datleminh5173-sys/ugv/ugv_jga25_v2/preview_ball_socket_fixed.png

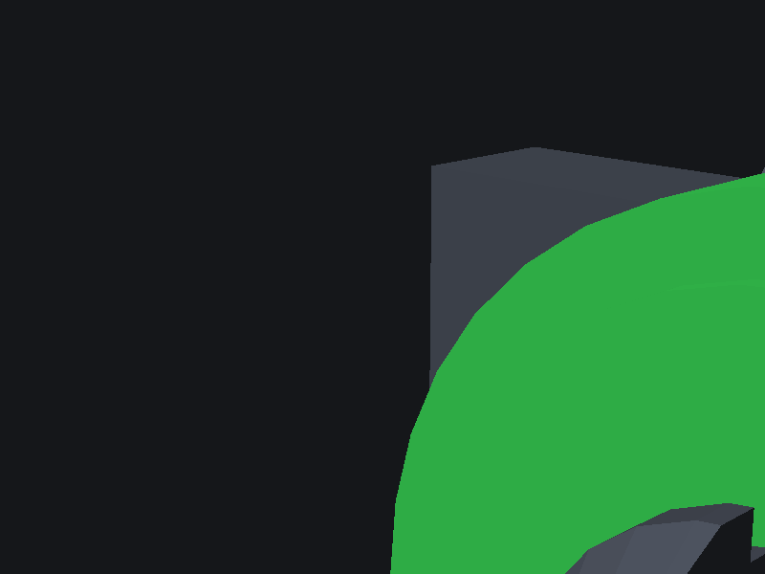
ugv_jga25_v2/preview_ball_socket_fixed.png
