datleminh5173-sys/ugv/ugv_jga25_v2/preview_ball_stud_angled.png

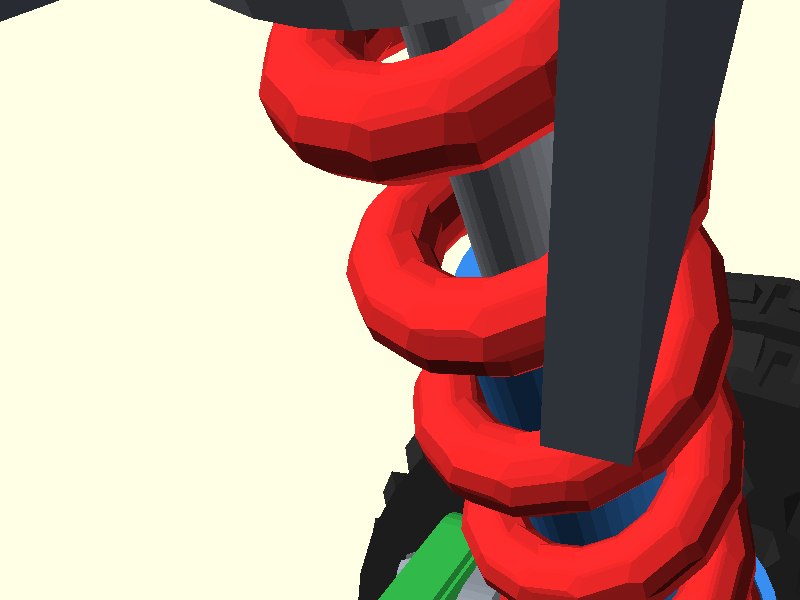
ugv_jga25_v2/preview_ball_stud_angled.png
