datleminh5173-sys/ugv/ugv_jga25_v2/preview_chot_snap_pin_single.png

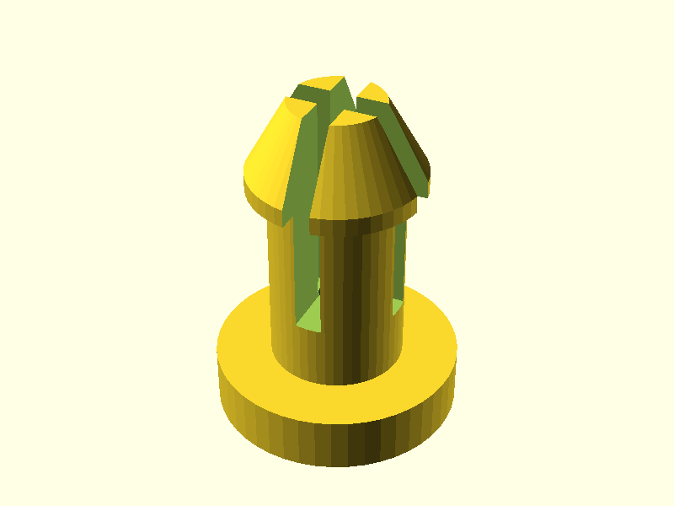
ugv_jga25_v2/preview_chot_snap_pin_single.png
