datleminh5173-sys/ugv/ugv_jga25_v2/preview_khop_cau_full_xe.png

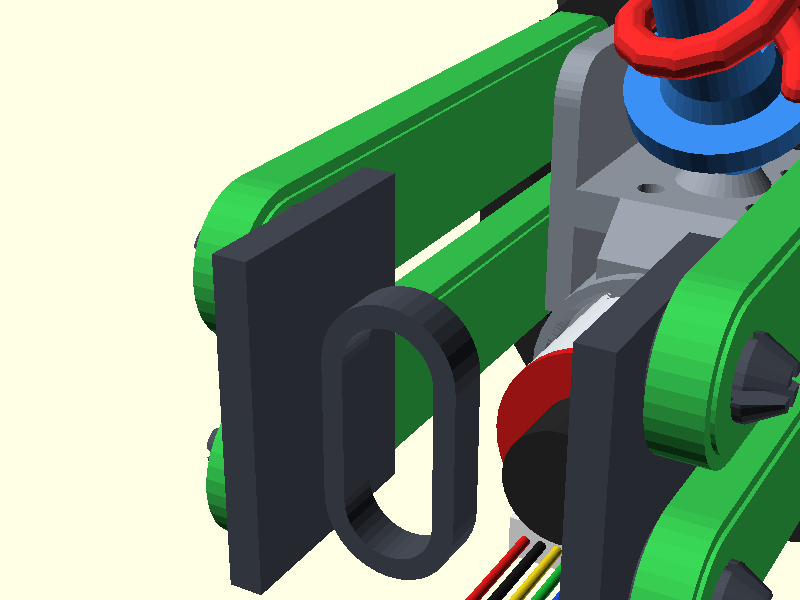
ugv_jga25_v2/preview_khop_cau_full_xe.png
