datleminh5173-sys/ugv/ugv_jga25_v2/preview_no_handles.png

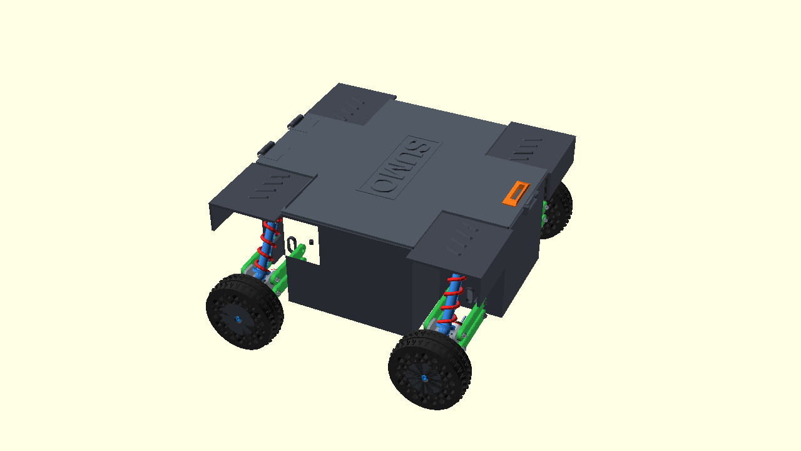
ugv_jga25_v2/preview_no_handles.png
