datleminh5173-sys/ugv/ugv_jga25_v2/preview_phuoc_khop_cau_bottom.png

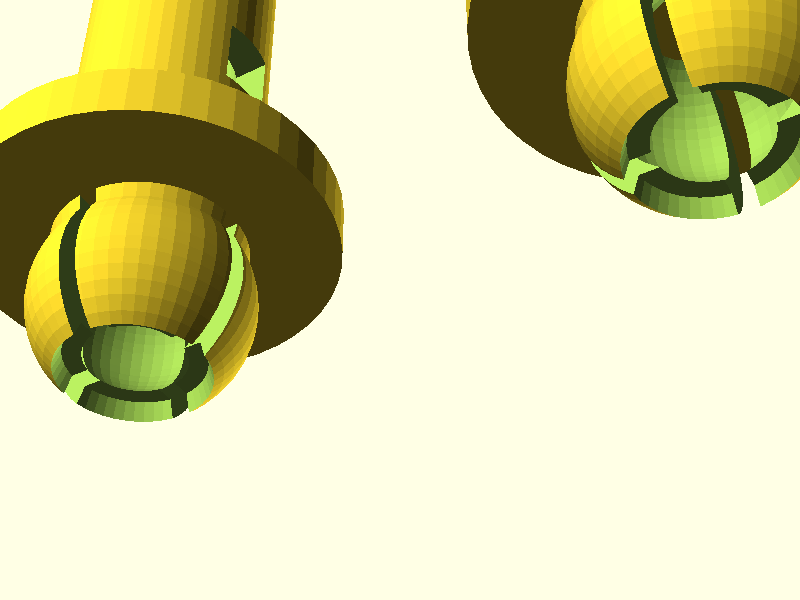
ugv_jga25_v2/preview_phuoc_khop_cau_bottom.png
