datleminh5173-sys/ugv/ugv_jga25_v2/preview_phuoc_snap_pin_close.png

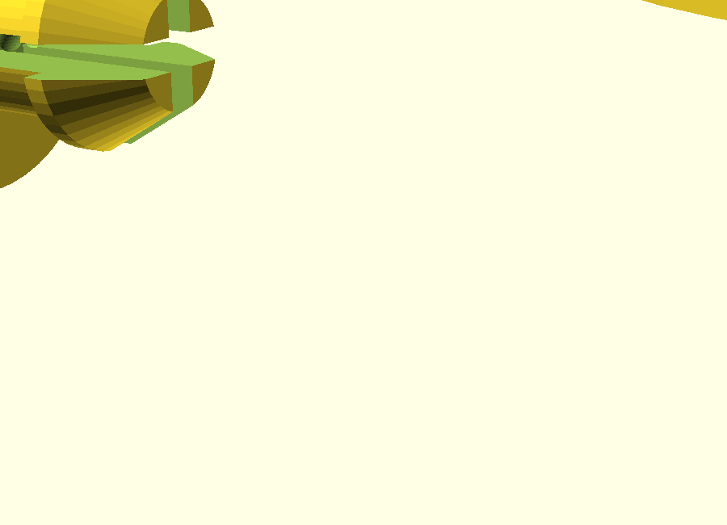
ugv_jga25_v2/preview_phuoc_snap_pin_close.png
