datleminh5173-sys/ugv/ugv_jga25_v2/preview_phuoc_snaplock.png

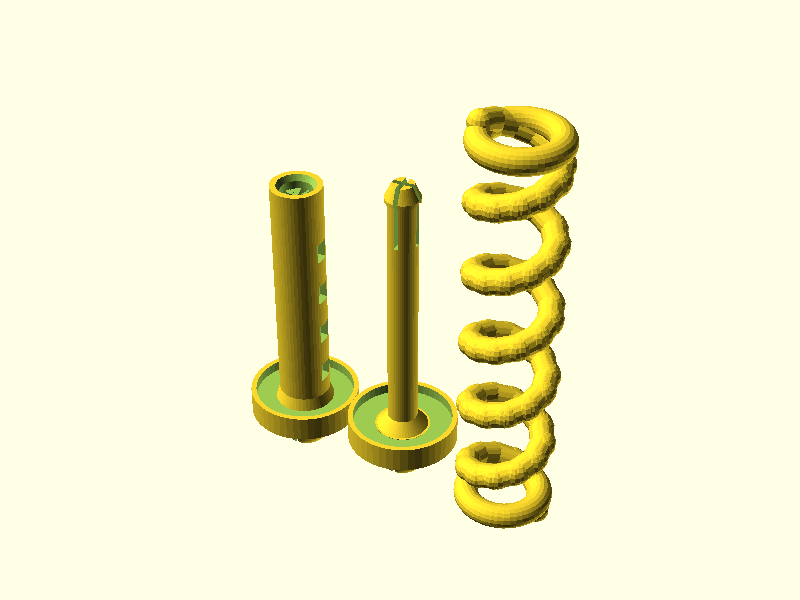
ugv_jga25_v2/preview_phuoc_snaplock.png
