datleminh5173-sys/ugv/ugv_jga25_v2/preview_snap_pins_closeup.png

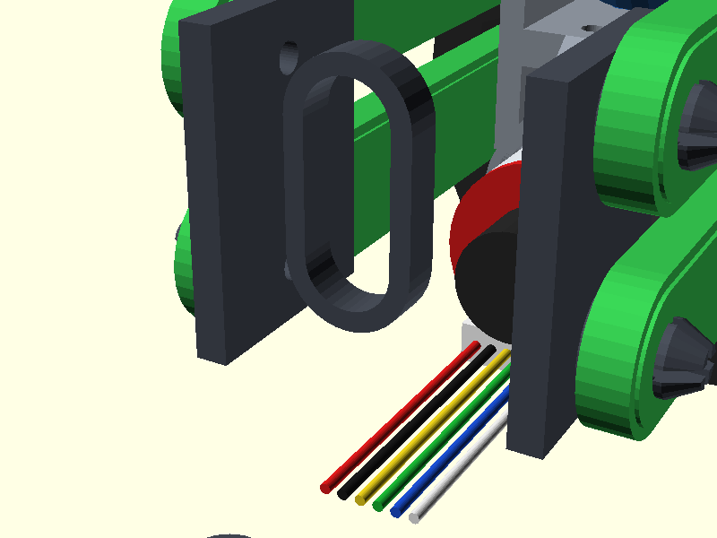
ugv_jga25_v2/preview_snap_pins_closeup.png
