datleminh5173-sys/ugv/ugv_jga25_v2/preview_spring_top_flat.png

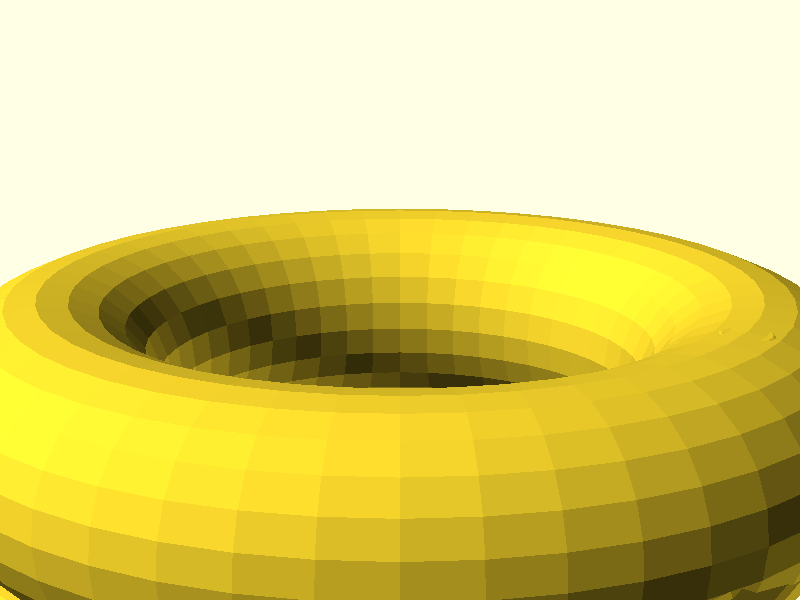
ugv_jga25_v2/preview_spring_top_flat.png
