datleminh5173-sys/ugv/ugv_my1016z_250w/images/01_MY1016Z_Thong_So_Tong_Quan.png

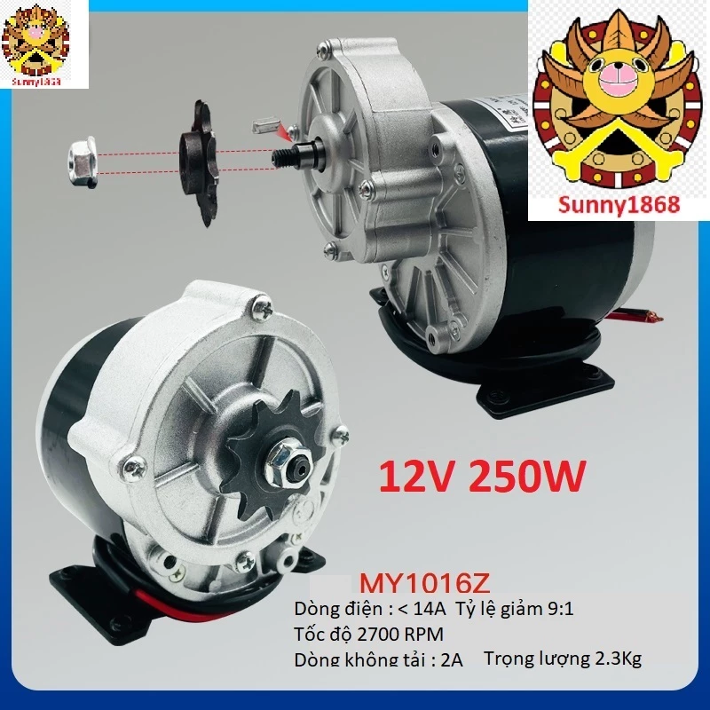
ugv_my1016z_250w/images/01_MY1016Z_Thong_So_Tong_Quan.png
