datleminh5173-sys/ugv/ugv_my1016z_250w/images/03_MY1016Z_Chan_De_Va_Bat_Ga.png

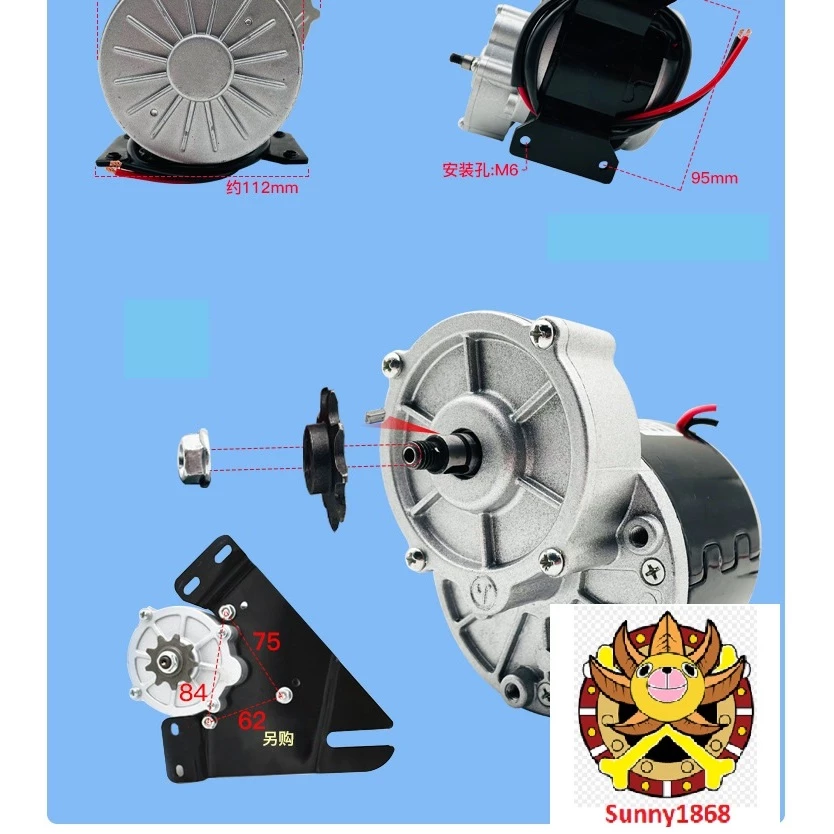
ugv_my1016z_250w/images/03_MY1016Z_Chan_De_Va_Bat_Ga.png
