datleminh5173-sys/ugv/ugv_my1016z_250w/images/04_Ban_Ve_Kich_Thuoc_Canh_Va_Chan_De.png

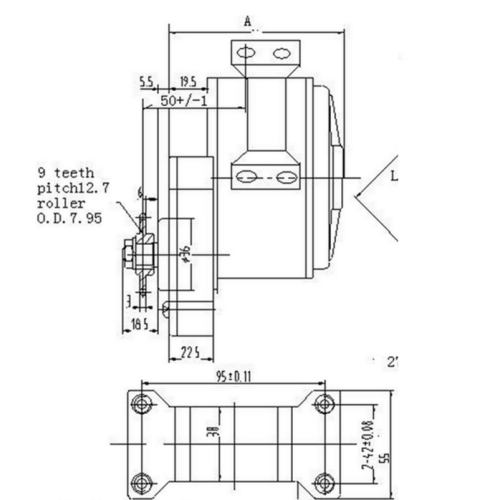
ugv_my1016z_250w/images/04_Ban_Ve_Kich_Thuoc_Canh_Va_Chan_De.png
