datleminh5173-sys/ugv/ugv_my1016z_250w/images/05_Ban_Ve_Mat_Truoc_Va_Tam_Lo.png

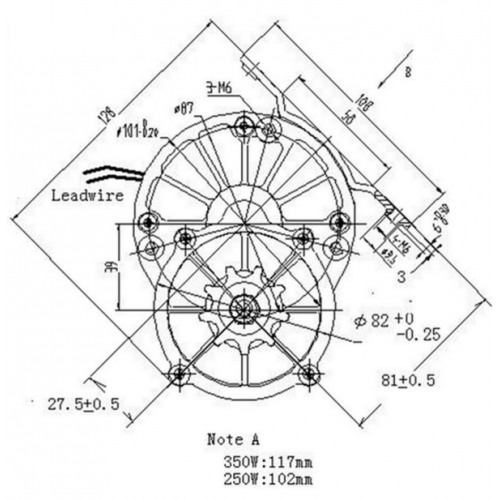
ugv_my1016z_250w/images/05_Ban_Ve_Mat_Truoc_Va_Tam_Lo.png
