datleminh5173-sys/ugv/ugv_my1016z_250w/images/07_Anh_Thuc_Te_Nhan_Thong_So.png

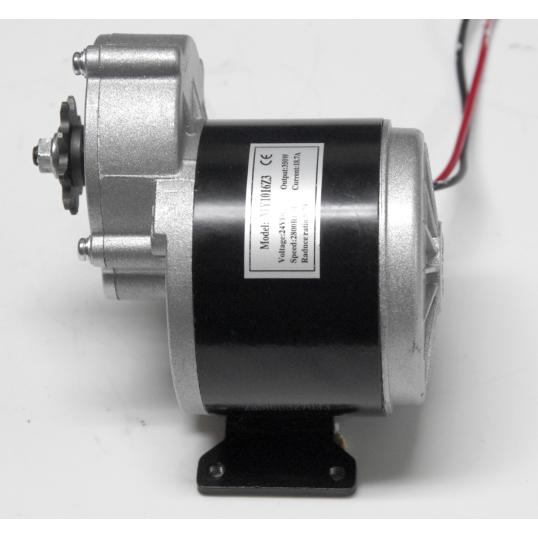
ugv_my1016z_250w/images/07_Anh_Thuc_Te_Nhan_Thong_So.png
