datleminh5173-sys/ugv/ugv_my1016z_250w/images/08_Ban_Ve_CAD_Chi_Tiet_Goc_Nghieng_15Do.png

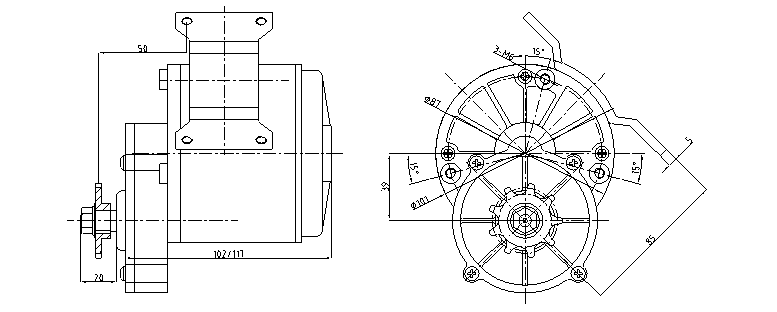
ugv_my1016z_250w/images/08_Ban_Ve_CAD_Chi_Tiet_Goc_Nghieng_15Do.png
