datleminh5173-sys/ugv/ugv_my1016z_250w/images/tyhe/TYHE_MY1016Z_02_Side_View.jpg

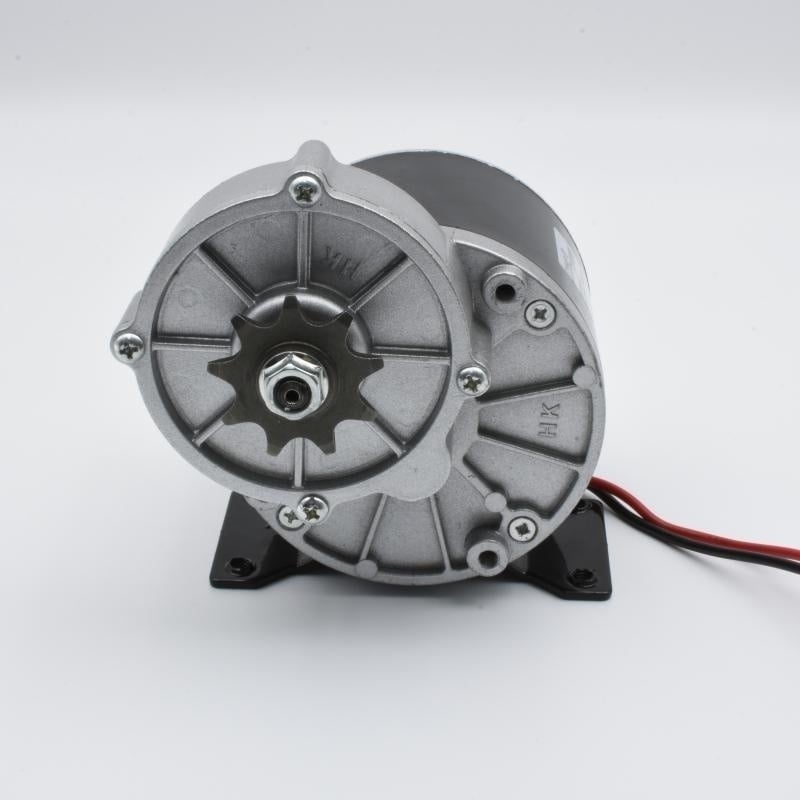
ugv_my1016z_250w/images/tyhe/TYHE_MY1016Z_02_Side_View.jpg
