datleminh5173-sys/ugv/ugv_my1016z_250w/images/tyhe/TYHE_MY1016Z_03_Rear_Angle.jpg

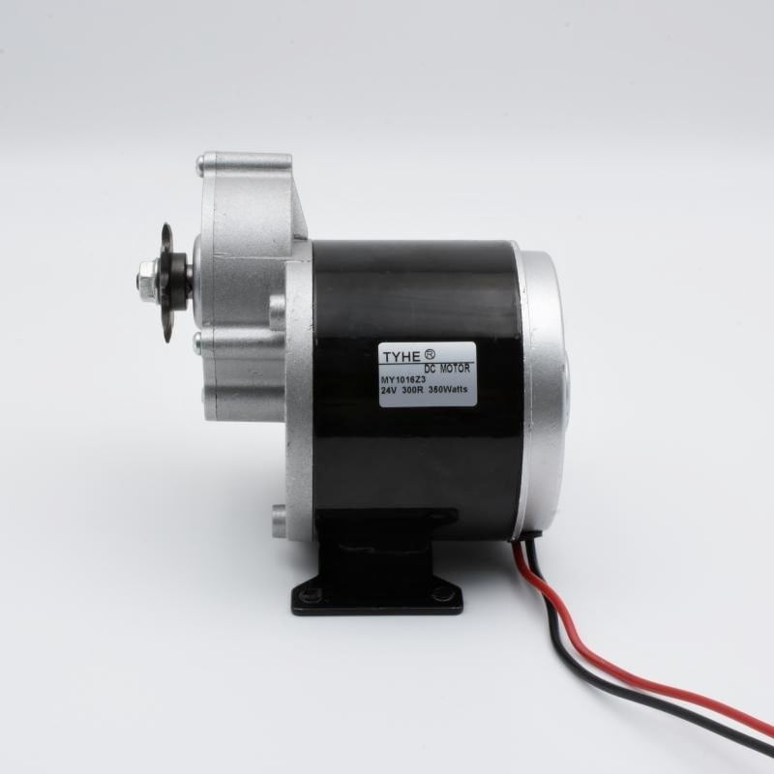
ugv_my1016z_250w/images/tyhe/TYHE_MY1016Z_03_Rear_Angle.jpg
