datleminh5173-sys/ugv/ugv_jga25_v2/preview_ga_dong_co_debug.png

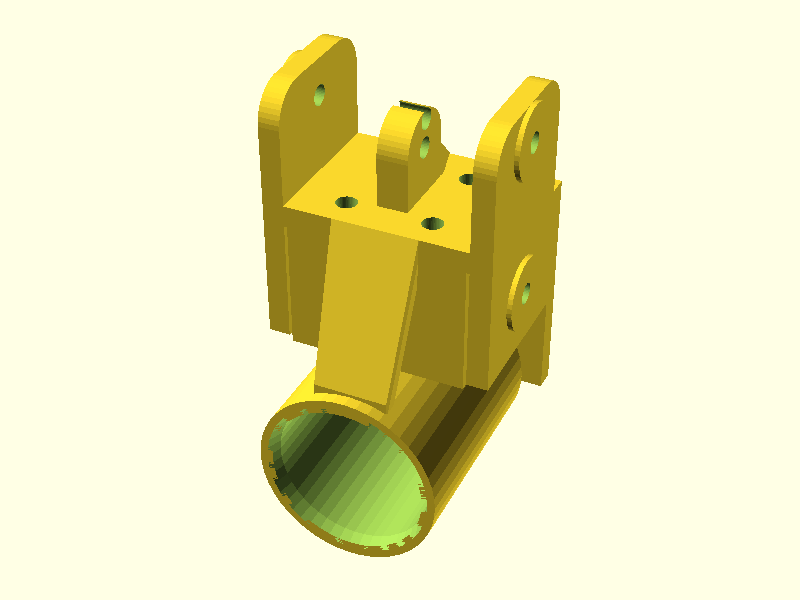
ugv_jga25_v2/preview_ga_dong_co_debug.png
